romkey/sensr-air/hw/air-stcc4/0.2.0/front.jpg

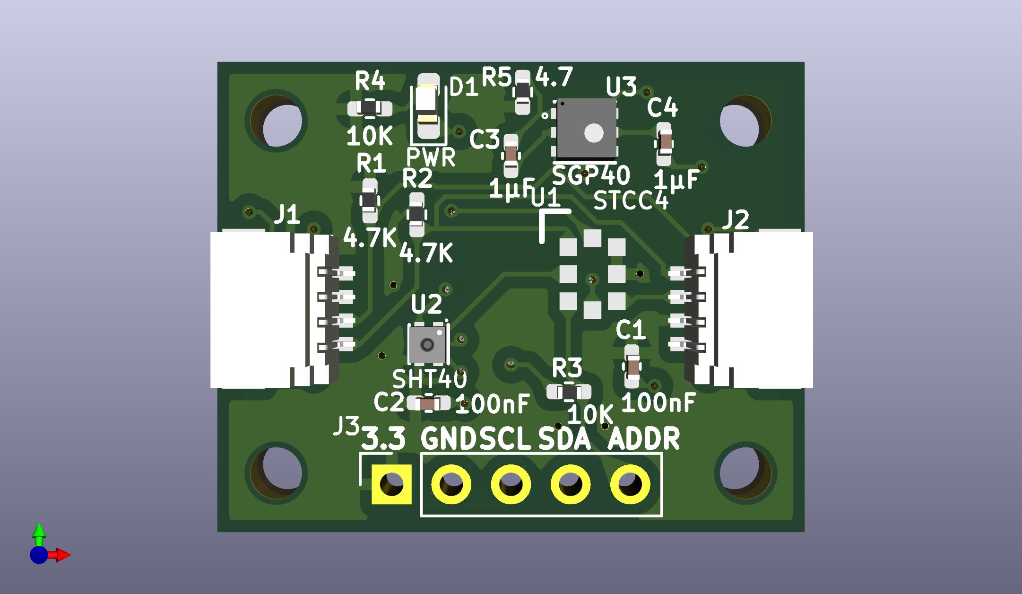
hw/air-stcc4/0.2.0/front.jpg
